MelansonTech/Dual-Isolated-Electronic-Load/Arduino/Eload PM and Display Controller REV 1.0/E-Load_Gen2_workspace/SetPointMinMaxUpdate.ino

void SetPointMinMaxUpdate(void) {

  switch (LDA.Mode.range) {

    case 0: //CC Load

      switch (LDA.volt.range) {

        case 0: //HV Range

          LDA.CurrentMax = 0.35;
          LDA.CurrentMin = 0;

          break;

        case 1: //MV Range

          switch (LDA.current.range) {

            case 0: // LC Range

              LDA.CurrentMax = 0.35;
              LDA.CurrentMin = 0;

              break;

            case 1: // MC Range

              LDA.CurrentMax = 3;
              LDA.CurrentMin = 0;
              break;
          }
          break;

        case 2: //LV Range

          switch (LDA.current.range) {

            case 0: // LC Range

              LDA.CurrentMax = 0.35;
              LDA.CurrentMin = 0;

              break;

            case 1: // MC Range

              LDA.CurrentMax = 3;
              LDA.CurrentMin = 0;

              break;

            case 2:

              LDA.CurrentMax = 10;
              LDA.CurrentMin = 0;

              break;

          }

          break;
      }

      break;

    case 1: //CR Load

      switch (LDA.volt.range) {

        case 0: //HV Range

          LDA.CurrentMax = 5000;
          LDA.CurrentMin = 1150;

          break;

        case 1: //MV Range

          switch (LDA.current.range) {

            case 0: // LC Range

              LDA.CurrentMax = 1500;
              LDA.CurrentMin = 170;

              break;

            case 1: // MC Range

              LDA.CurrentMax = 150;
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
              break;

            case 2:
              LDB.CurrentMax = 50;
              LDB.CurrentMin = 2;
              break;
          }
      }

      break;

    case 2: //CP Load

      LDB.CurrentMax = 200;
      LDB.CurrentMin = 0;
      
      break;

  }
}
