MelansonTech/Dual-Isolated-Electronic-Load/Arduino/E-Load_Gen2_workspace/functions/LDA_Disable.ino

void LDA_Disable(void){
  
//digitalWrite(LDA_LED, LOW);            
//digitalWrite(LDA_GC,HIGH);


//LDA_GC_ONOFF = 0;  // note: these varibles do nothing at the moment          
//LDA_LED_ONOFF = 0;



           
 }      
