MelansonTech/Dual-Isolated-Electronic-Load/Arduino/E-Load_Gen2_workspace/functions/LDB_Disable.ino

 void LDB_Disable(void){
  
//          digitalWrite(LDB_LED, LOW);             
//          digitalWrite(LDB_GC,HIGH);
                    
//          LDB_GC_ONOFF = 0;      // note: these varibles do nothing at the moment      
//          LDB_LED_ONOFF = 0;
          
          
 }      
        
