MelansonTech/Dual-Isolated-Electronic-Load/Arduino/E-Load_Gen2_workspace/functions/LDB_Enable.ino

void LDB_Enable(void){          
       
          
//          LDB_GC_ONOFF = 1;      // note: these varibles do nothing at the moment   
////          LDB_LED_ONOFF = 1;         
////          digitalWrite(LDB_LED,HIGH); 

        
}
