MelansonTech/Dual-Isolated-Electronic-Load/Arduino/E-Load_Gen2_workspace/functions/LoadB_ON_OFFPopCallback.ino

void LoadB_ON_OFFPopCallback(void *ptr)  // Release event for dual state button bt1
{
  
//   uint32_t BTstate = 0;   // Create variable to store value we are going to get
//   LoadB_ON_OFF.getValue(&BTstate);  // Read value of dual state button to know the state (0 or 1)

//  if(BTstate == 1){  // If dual state button is equal to 1 (meaning is ON)...
//    digitalWrite(LDB_LED, HIGH);  // Turn ON internal LED
//  }else{  // Since the dual state button is OFF...
//    digitalWrite(LDB_LED, LOW);  // Turn OFF internal LED
//  }

}  // End of release event
