MelansonTech/Dual-Isolated-Electronic-Load/Arduino/E-Load_Gen2_workspace/functions/PgSelAutoPopCallback.ino

// Page change event:
void PgSelAutoPopCallback(void *ptr)  // If page 0 is loaded on the display, the following is going to execute:
{
  //CurrentPage = 2;  // temp assignment to pg 2
}  // End of press event
