MelansonTech/Dual-Isolated-Electronic-Load/Arduino/E-Load_Gen2_workspace/functions/PgSelStaticPopCallback.ino

// Page change event:
void PgSelStaticPopCallback(void *ptr)  // If page 0 is loaded on the display, the following is going to execute:
{
  //CurrentPage = 2;  // Set variable as 0 so from now on arduino knows page 0 is loaded on the display
}  // End of press event
