MelansonTech/Dual-Isolated-Electronic-Load/Arduino/Eload PM and Display Controller REV 1.0/E-Load_Gen2_workspace/loadOnOffUpdateFunc.ino

void loadOnOffUpdateFunc(int address, int OnOffState) {

    if (OnOffState == 1) {

      DBserial.println("Load A ONOFF state Change");
    
        Wire.beginTransmission(address); //U1B
        Wire.write(onOffStateChange);
        Wire.write(OnOffState);   // sends instruction byte
        Wire.endTransmission();     // stop transmitting

      }

      else {

        Wire.beginTransmission(address); //U1B
        Wire.write(onOffStateChange);
        Wire.write(OnOffState);   // sends instruction byte
        Wire.endTransmission();     // stop transmitting

      }
    }
  

 
